krwc/nixie/boost-converter.asc

C1: cap; 680p
C2: cap; 3.3µ
C3: cap; 220µ
D1: diode; 1N914
D2: diode; BAS21HM
L1: ind; 100µ
M1: nmos; IRFP90N20D
Q1: pnp; 2N3906
R1: res; 1k
R2: res; 475k
R3: res; 3.1k
R4: res; 0.22
R5: res; 10k
U1: mc34063
V1: voltage; 12; Rser=0.01
Named nets: 0, Vcc
.tran 10ms uic
.inc mc34063.lib
.options Gmin=1e-9  method=Gear
